mige69/Microchip-Hcs-200-1-300-1-320-Keeloq-Programmer/hcs/IMG_20220124_160551.jpg

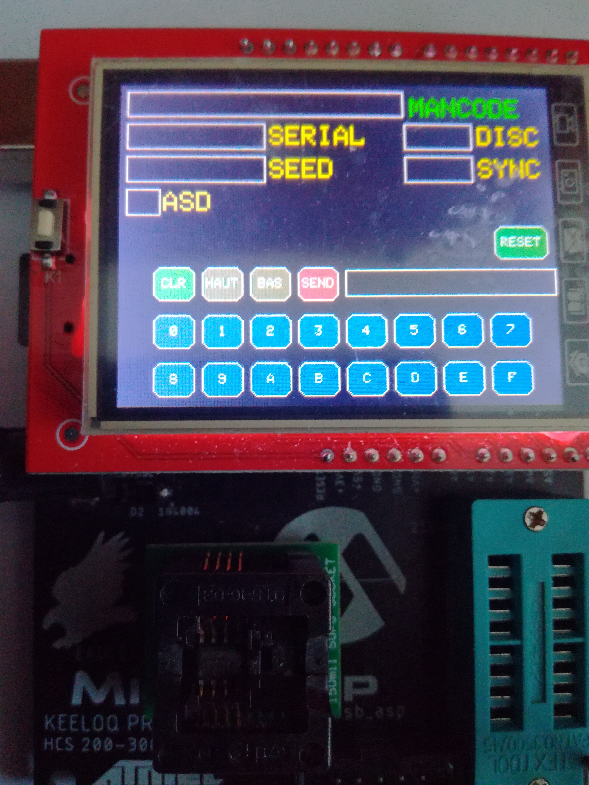
hcs/IMG_20220124_160551.jpg
